Lenbok/scad-keyboard-cases/crkbd/stls/crkbd-case-carrier.stl

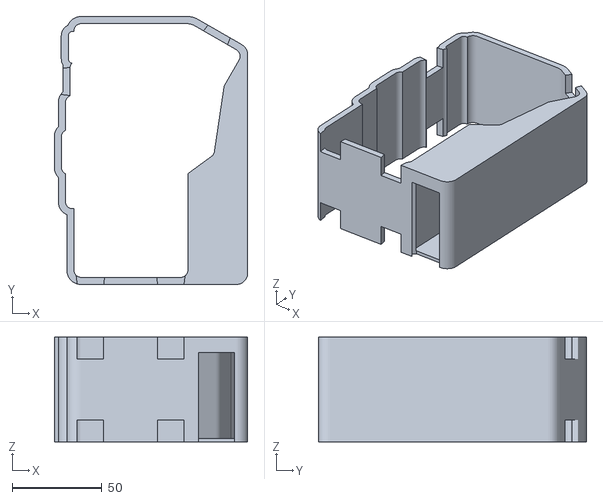
[picture p26: CAD file, 2019-06-18]
crkbd/stls/crkbd-case-carrier.stl
107.9 x 149.5 x 58.4
