Lenbok/scad-keyboard-cases/crkbd/stls/crkbd-case-carrier-door-0.3.stl

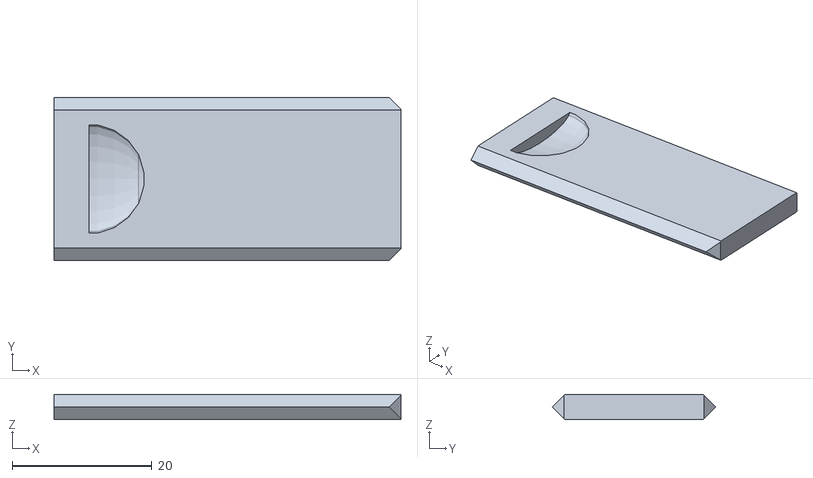
[picture p27: CAD file, 2019-06-18]
crkbd/stls/crkbd-case-carrier-door-0.3.stl
49.7 x 23.4 x 3.60
