Lenbok/scad-keyboard-cases/crkbd/stls/crkbd-case-bottom.stl

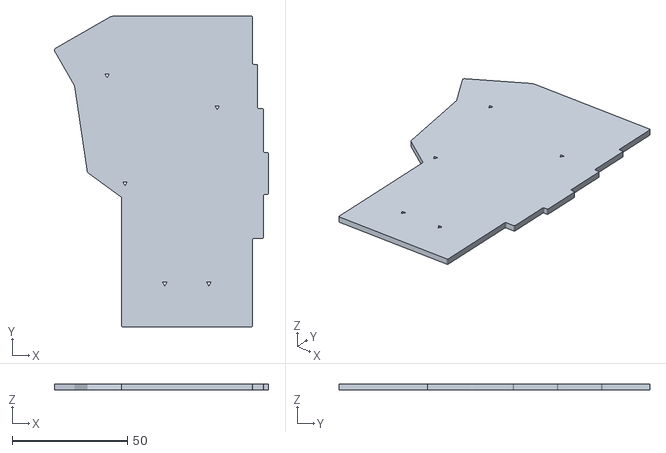
[picture p28: CAD file, 2019-04-19]
crkbd/stls/crkbd-case-bottom.stl
92.8 x 134.7 x 2.50
