Lenbok/scad-keyboard-cases/crkbd/stls/crkbd-case-top.stl

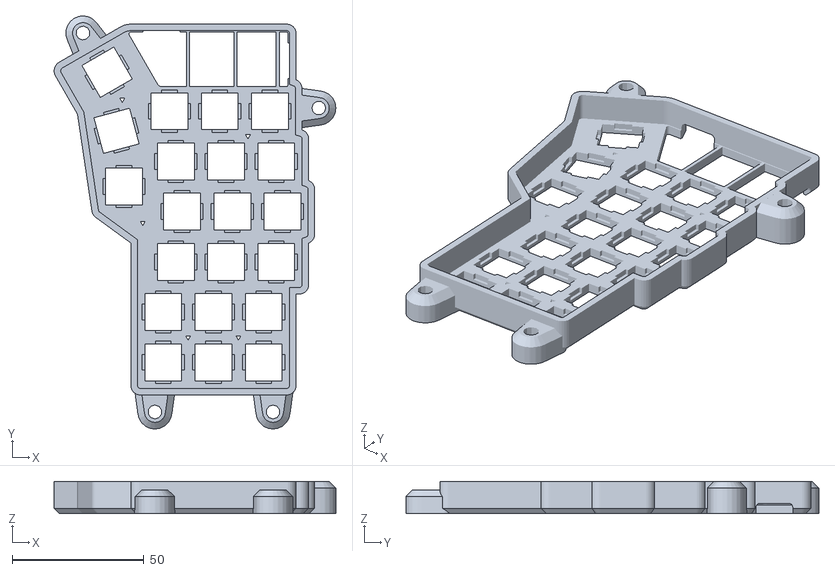
[picture p29: CAD file, 2019-04-19]
crkbd/stls/crkbd-case-top.stl
106.9 x 156.7 x 12.2
