Lenbok/scad-keyboard-cases/humla/humla-case.scad

// Cases for humla keyboard.
//
// Two main versions:
//
// - A simple bumper case.
//
// - A case that includes an adaptor that lets the humla sit nicely over the
//   top of the existing keyboard of my laptop laptop.

include <kle/hp-zbook.scad>
include <kle/macbook-pro-2015.scad>
include <../keyboard-case.scad>

$fa = 0.5;
$fs = $preview ? 5 : 1;

eps = 0.01;

// Parameters for the hp zbook keyboard for the adaptor
laptop_hp_zbook = [hp_zbook, 18.68, 1.3, 2.5, [0, 0], 1];
// Parameters for the 2015 macbook pro keyboard for the adaptor
laptop_macbook = [macbook_pro_2015, 19, 2.0, 2.7, [0, 1.25], 0.97];

function laptop_layout(laptop) = laptop[0];     // key layout
function unit(laptop) = laptop[1];              // key spacing
function key_depth(laptop) = laptop[2];         // key depth
function key_channel_width(laptop) = laptop[3]; // key channel width
function layout_offset(laptop) = laptop[4];     // overall offset
function layout_yscale(laptop) = laptop[5];     // for non-square laptop unit size!

laptop = laptop_hp_zbook;
//laptop = laptop_macbook;


outer_thickness = 2;   // Thickness of the outer wall of the bumper
base_thickness = 1.0;  // Thickness of the base
humla_thickness = 3.0; // Depth to ensure flush with top of humla pcb (i.e. thickness of pcb plus any rear protruberances)
pcb_tol = 0.5;        // Tolerance between pcb and bumper side wall
case_thickness = base_thickness + humla_thickness;


// 2d profile of the humla PCB. SVG extracted from kicad and painfully manipulated into something OpenSCAD could load
// This is also translated to overlap nicely with where the laptop keyboard will be
module humla_pcb(mcu_extra = false) {
    translate(v = [31, -107.5, 0]) resize([210, 0, 0],  auto = true) import(file = "orig/humla-base-plate-outline.svg");
    if (mcu_extra) {
        mcu_switch_profile();
    }
}

module case_key_hole(size) {
    offset(delta = -key_channel_width(laptop) / 2, chamfer = false) square(size * unit(laptop), center = true);
}

module key_holes(keys, type = "both") {
    // Mirror because KLE has Y axis reversed
    translate(v = layout_offset(laptop)) mirror([0, 1, 0]) for (key = keys) {
        scale([1, layout_yscale(laptop)]) position_key(key, unit = unit(laptop))
            case_key_hole(key_size(key));
    }
}

module mcu_switch_position() {
    translate(v = [111.5, -34.3, 0])  rotate([0, 0, -13]) children();
}
module mcu_switch_profile() {
    mcu_switch_position() translate(v = [0, -0.5]) square([4, 12], center = true);
}
// Rebate for access to MCU on/off switch
module mcu_switch_cutout() {
    mcu_switch_position() translate(v = [-outer_thickness/2 - pcb_tol, 0, 4 - eps]) cube([outer_thickness, 12, 10], center = true);
}

// A plate containing cutouts corresponding to the laptop key positions. This will position the humla
// and stop it sliding around
module laptop_keyboard_adaptor_plate() {
    difference() {
        union() {
            // Laptop key cutouts
            linear_extrude(height = key_depth(laptop), center = false, convexity = 10, twist = 0, slices = 20, scale = 1.0) difference() {
                offset(r = outer_thickness, chamfer = false) humla_pcb();
                key_holes(laptop_layout(laptop), type = "plate");
            }
            // base plate
            translate(v = [0, 0, key_depth(laptop) - eps]) {
                linear_extrude(height = base_thickness, center = false, convexity = 10, twist = 0, slices = 20, scale = 1.0) {
                    offset(r = outer_thickness, chamfer = false) humla_pcb();
                }
            }
        }
        mcu_switch_cutout();
    }
}

// A simple bumper case for the humla. This can be glued to the top of the laptop adaptor plate.
module humla_bumper_case() {
    translate(v = [0, 0, key_depth(laptop) - eps])
        difference() {
        //linear_extrude(height = case_thickness) {
        chamfer_extrude(height = case_thickness, faces = "top") {
            offset(r = outer_thickness, chamfer = false) humla_pcb();
        }
        translate(v = [0, 0, base_thickness]) {
            linear_extrude(height = humla_thickness + eps, center = false, convexity = 10, twist = 0, slices = 20, scale = 1.0) {
                offset(delta = pcb_tol, chamfer = false) humla_pcb();
            }
        }
        mcu_switch_cutout();
    }
}

module bumper_case_case() {
    top_case_clearance = 18.5;
    difference() {
        chamfer_extrude(height = top_case_clearance + outer_thickness, faces = "top") {
            offset(r = outer_thickness * 2, chamfer = false) humla_pcb();
        }
        translate(v = [0, 0, -eps]) chamfer_extrude(height = case_thickness + base_thickness, faces = "top") {
            offset(r = outer_thickness + pcb_tol, chamfer = false) humla_pcb();
        }
        translate(v = [0, 0, base_thickness]) {
            linear_extrude(height = top_case_clearance, center = false, convexity = 10, twist = 0, slices = 20, scale = 1.0) {
                offset(delta = pcb_tol, chamfer = false) humla_pcb(true);
            }
        }
        translate(v = [0, 0, -eps]) chamfer_extrude(height = case_thickness + base_thickness + 1, faces = "top") {
            translate(v = [0, -70]) square(size = [300, 20], center = false);
        }
    }
}

part = "laptop-adaptor";
explode = 1;
if (part == "laptop-adaptor") {
    rotate(a = [0, 180, 45]) translate(v = [-135, 70, 0])
        laptop_keyboard_adaptor_plate();
} else if (part == "profile") {
    humla_pcb(true);
} else if (part == "bumper-case") {
    rotate(a = [0, 0, 45]) translate(v = [-135, 70, 0])
    humla_bumper_case();
} else if (part == "bumper-case-case") {
    bumper_case_case();
} else if (part == "assembled") {
    color("silver") laptop_keyboard_adaptor_plate();
    translate(v = [0, 0, base_thickness]) {
        color("red") humla_bumper_case();
        translate(v = [0, 0, key_depth(laptop) + case_thickness - 1]) color("#222222") linear_extrude(height = 1) humla_pcb();
        translate(v = [0, 0, 20]) bumper_case_case();
    }
 }

// Requires my utility functions in your OpenSCAD lib or as local submodule
// https://github.com/Lenbok/scad-lenbok-utils.git
use<../Lenbok_Utils/utils.scad>
